Thunderdropmusic/MarcaPasos/docs/assets/1775234487619.jpg

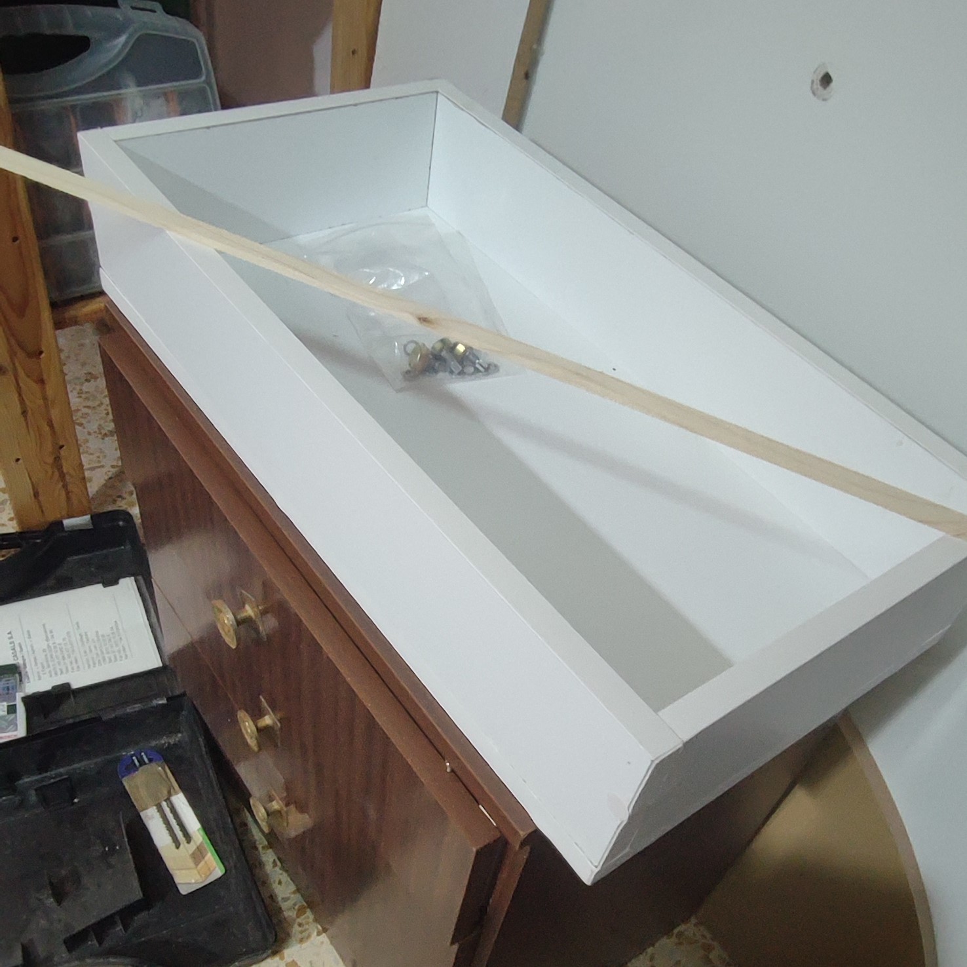
docs/assets/1775234487619.jpg
