Thunderdropmusic/MarcaPasos/docs/assets/1775234487627.jpg

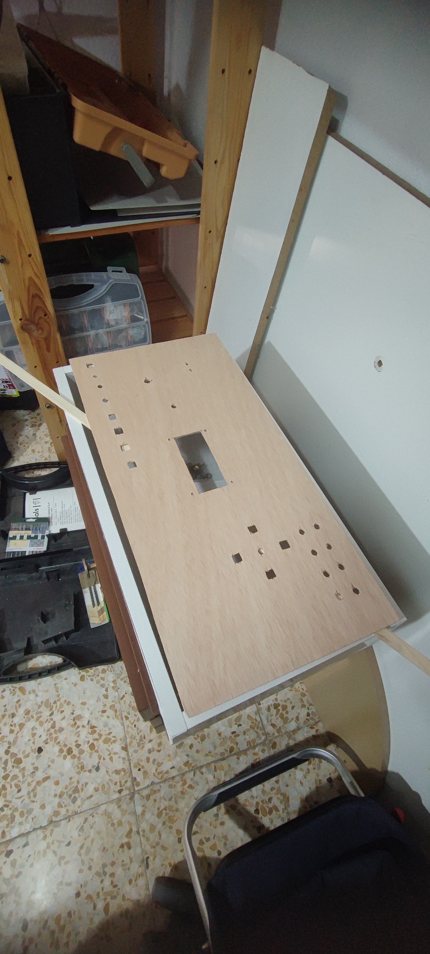
docs/assets/1775234487627.jpg
