Thunderdropmusic/MarcaPasos/docs/assets/1775234487634.jpg

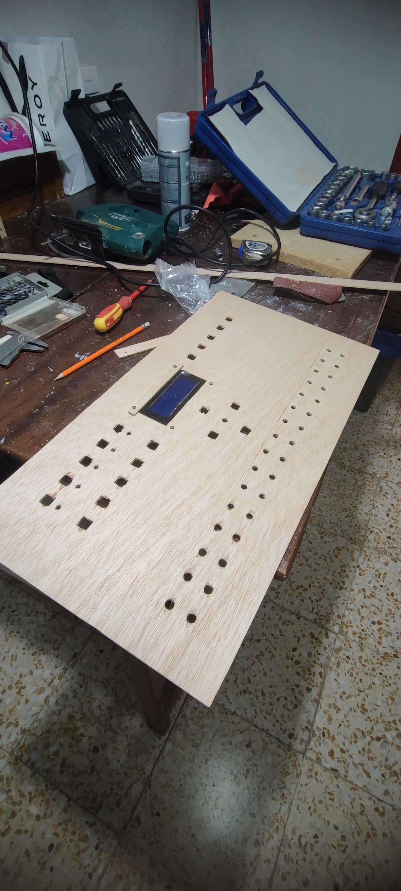
docs/assets/1775234487634.jpg
