Thunderdropmusic/MarcaPasos/docs/assets/1775234487641.jpg

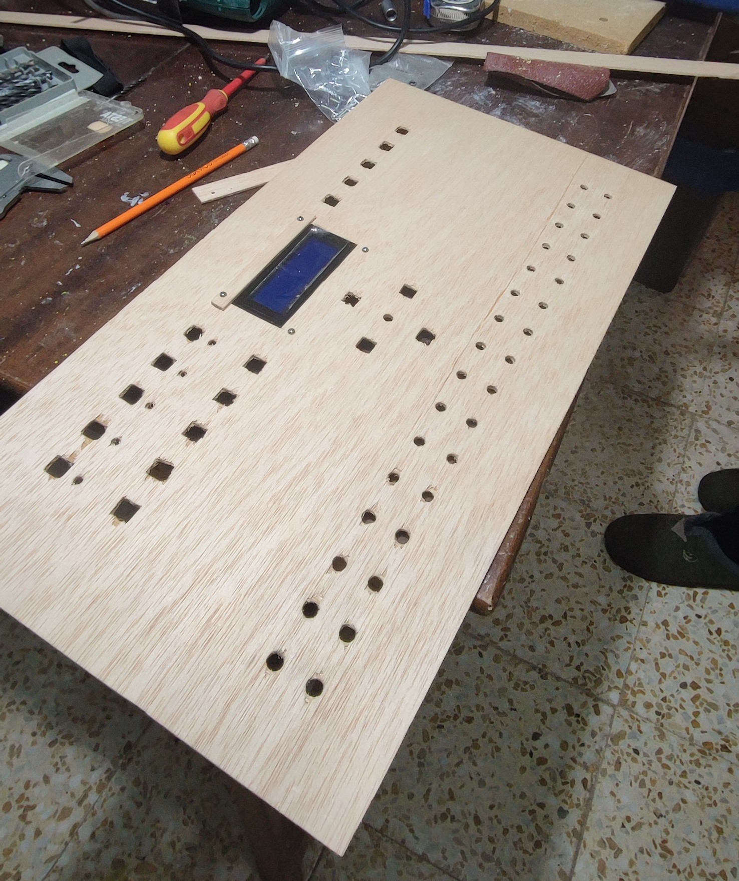
docs/assets/1775234487641.jpg
