Thunderdropmusic/MarcaPasos/docs/assets/1776208259461.jpg

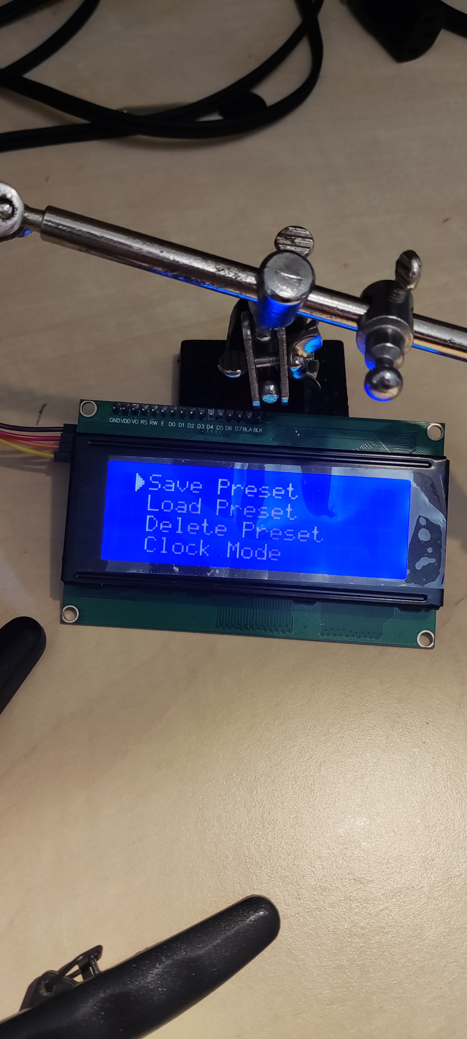
docs/assets/1776208259461.jpg
