Thunderdropmusic/MarcaPasos/docs/assets/1776208259470.jpg

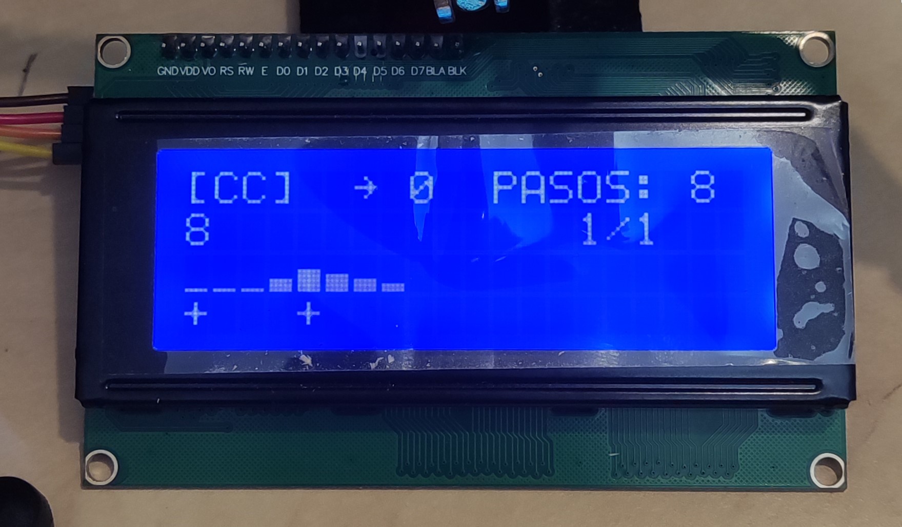
docs/assets/1776208259470.jpg
