Thunderdropmusic/MarcaPasos/docs/assets/1776208259479.jpg

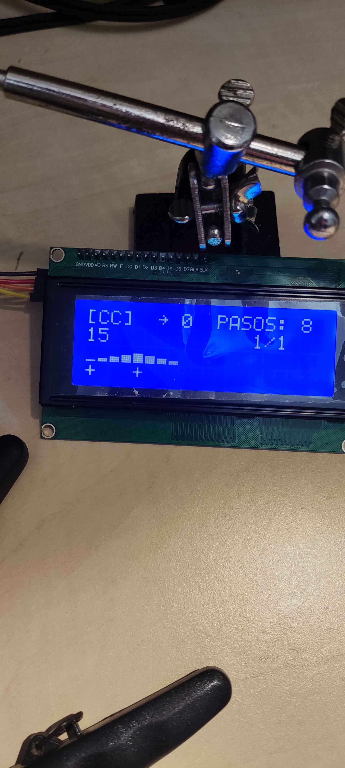
docs/assets/1776208259479.jpg
