Thunderdropmusic/MarcaPasos/docs/assets/1776208259487.jpg

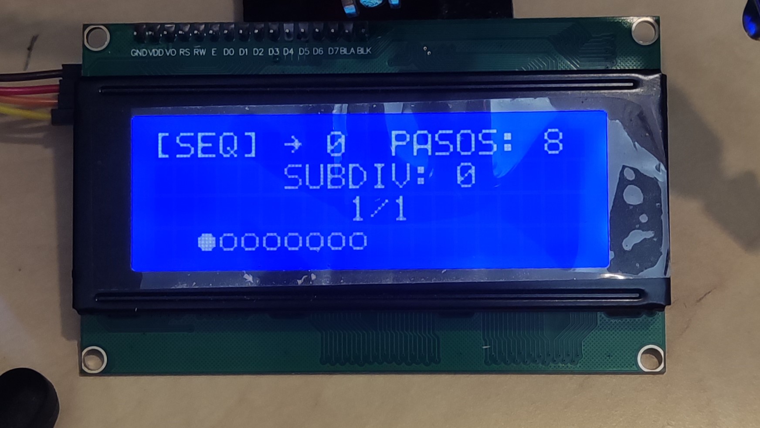
docs/assets/1776208259487.jpg
