Thunderdropmusic/MarcaPasos/docs/assets/1776208259495.jpg

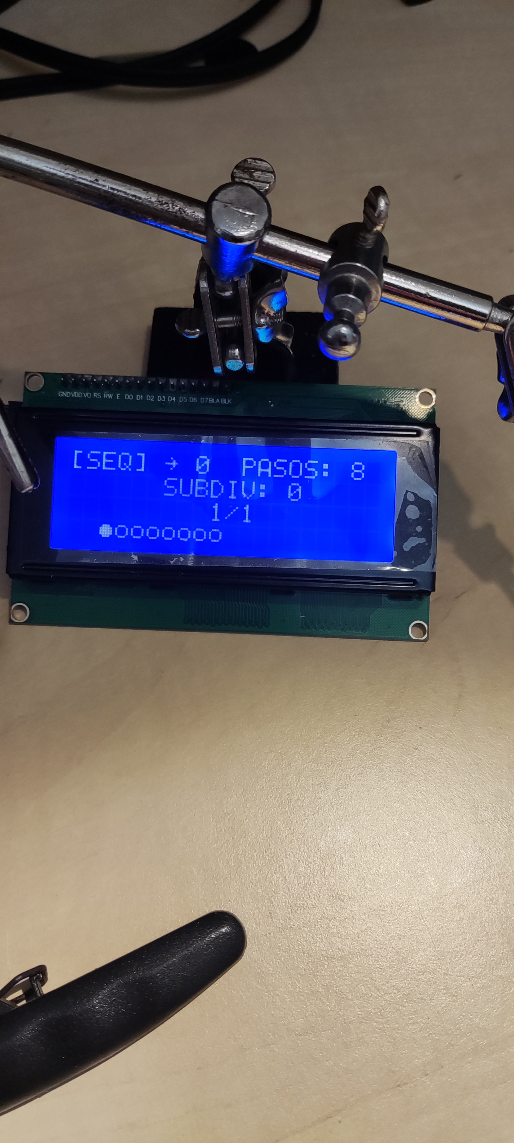
docs/assets/1776208259495.jpg
