Thunderdropmusic/MarcaPasos/docs/assets/1776208259502.jpg

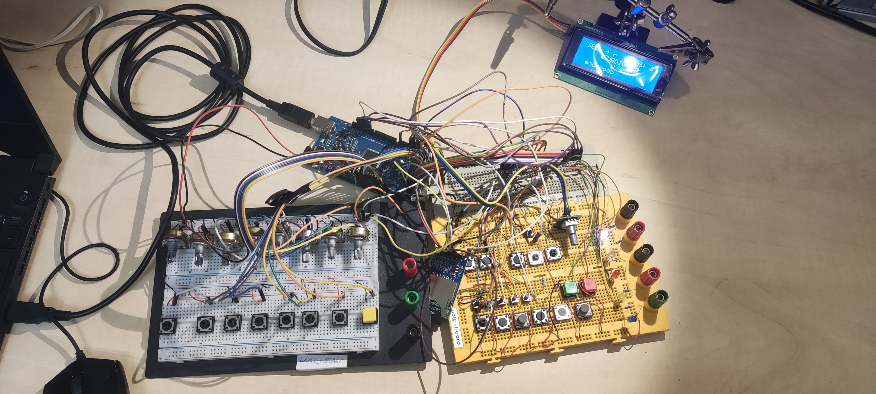
docs/assets/1776208259502.jpg
