Thunderdropmusic/MarcaPasos/docs/assets/1776288896708.jpg

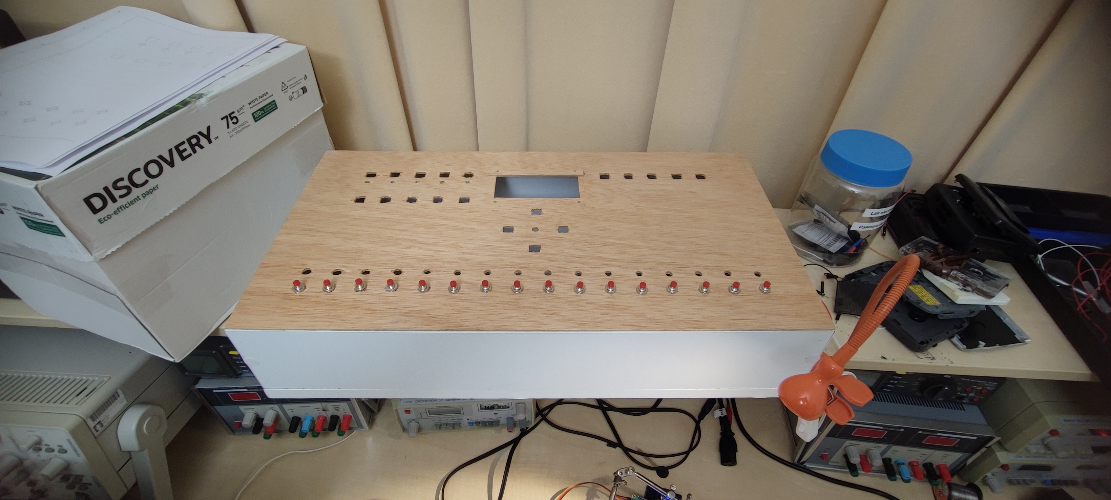
docs/assets/1776288896708.jpg
