Thunderdropmusic/MarcaPasos/docs/assets/1776288896717.jpg

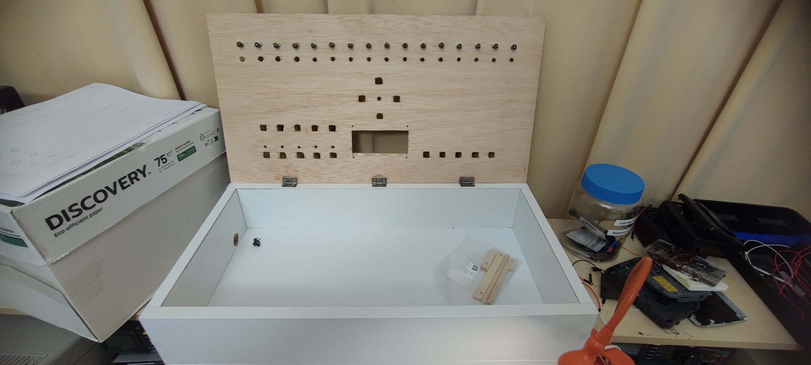
docs/assets/1776288896717.jpg
