Thunderdropmusic/MarcaPasos/docs/assets/1776288896731.jpg

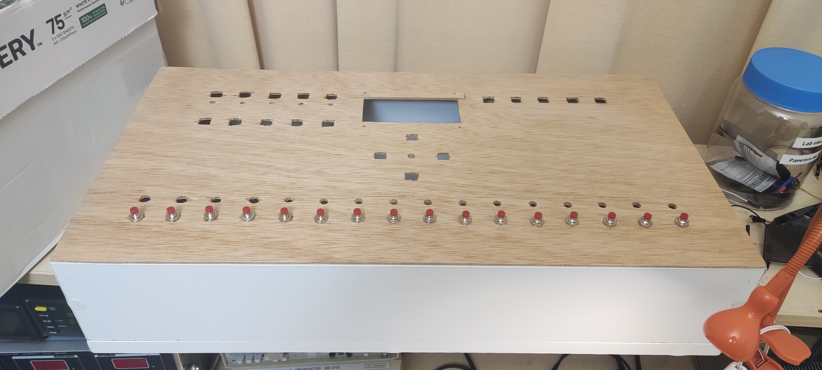
docs/assets/1776288896731.jpg
