Thunderdropmusic/MarcaPasos/docs/assets/1776289153111.jpg

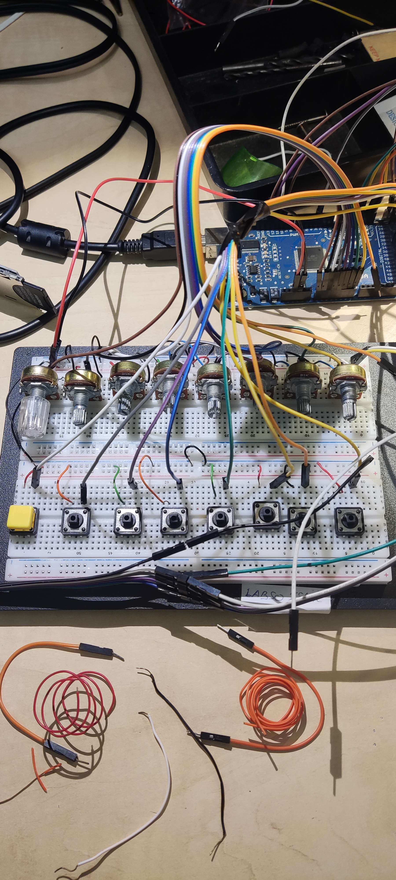
docs/assets/1776289153111.jpg
