Thunderdropmusic/MarcaPasos/docs/assets/1776289153119.jpg

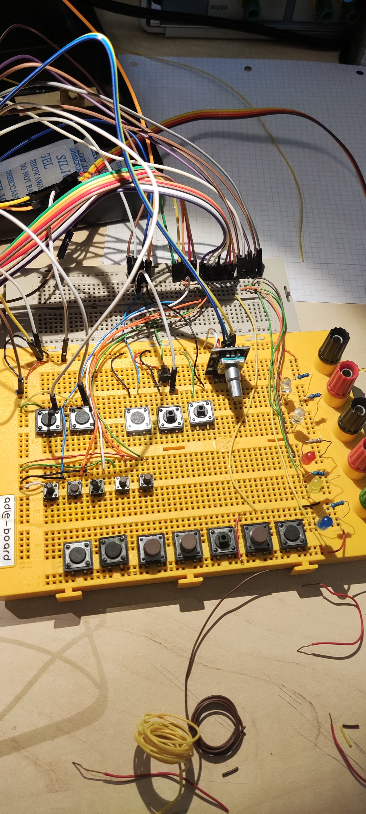
docs/assets/1776289153119.jpg
