Thunderdropmusic/MarcaPasos/docs/assets/1780314757962.jpg

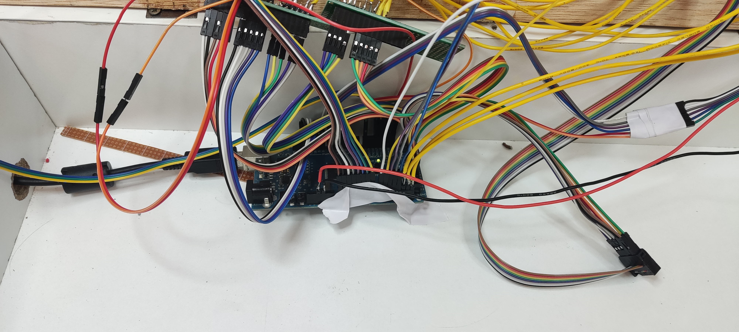
docs/assets/1780314757962.jpg
