Thunderdropmusic/MarcaPasos/docs/assets/1780314757989.jpg

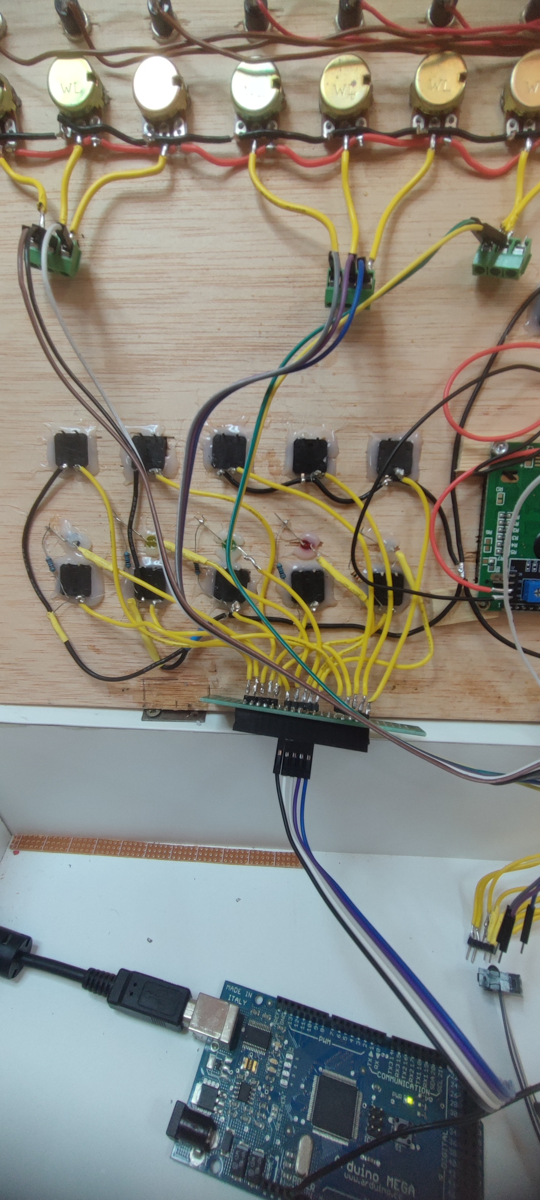
docs/assets/1780314757989.jpg
