Thunderdropmusic/MarcaPasos/docs/assets/1780314758041.jpg

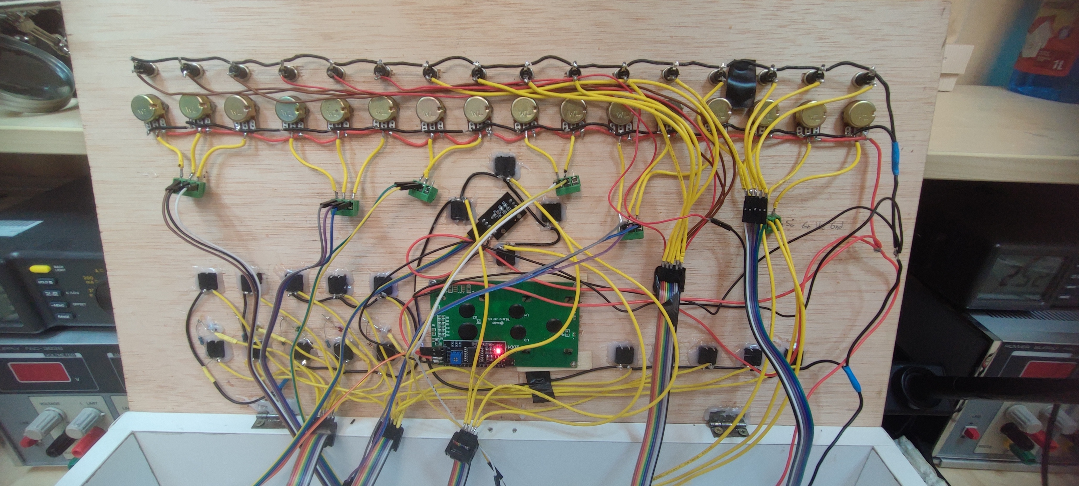
docs/assets/1780314758041.jpg
