Thunderdropmusic/MarcaPasos/docs/assets/1780314758049.jpg

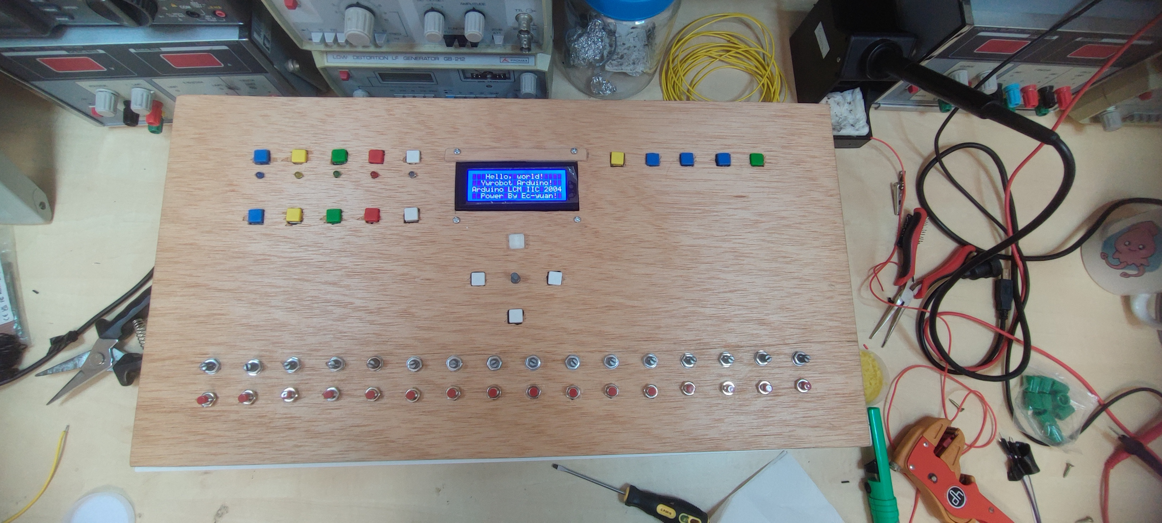
docs/assets/1780314758049.jpg
