Thunderdropmusic/MarcaPasos/docs/assets/1780314758056.jpg

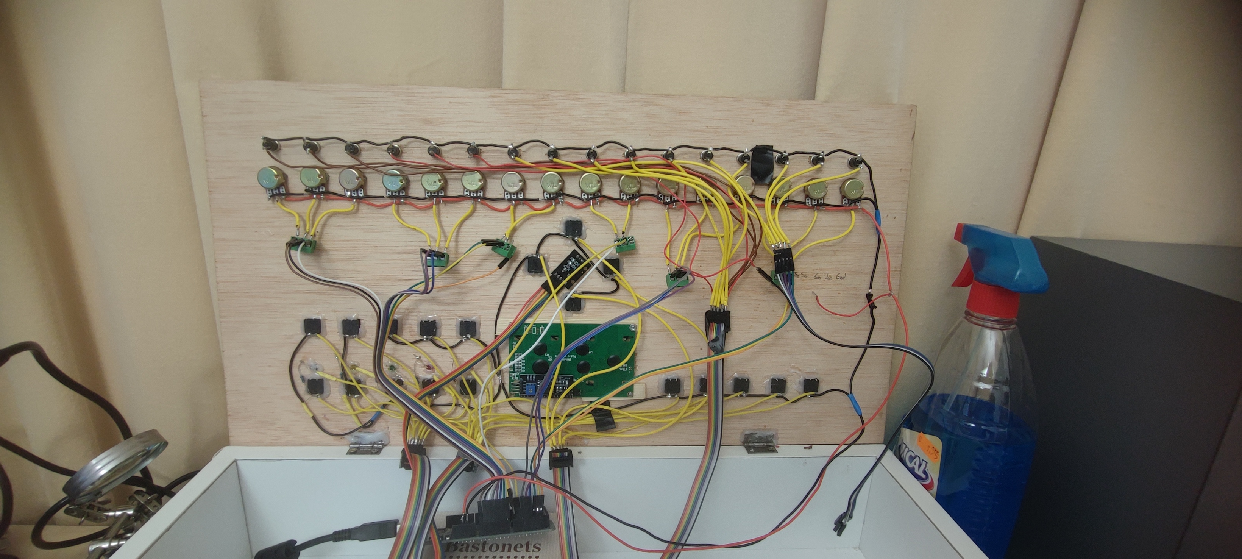
docs/assets/1780314758056.jpg
