Thunderdropmusic/MarcaPasos/docs/assets/1780314758062.jpg

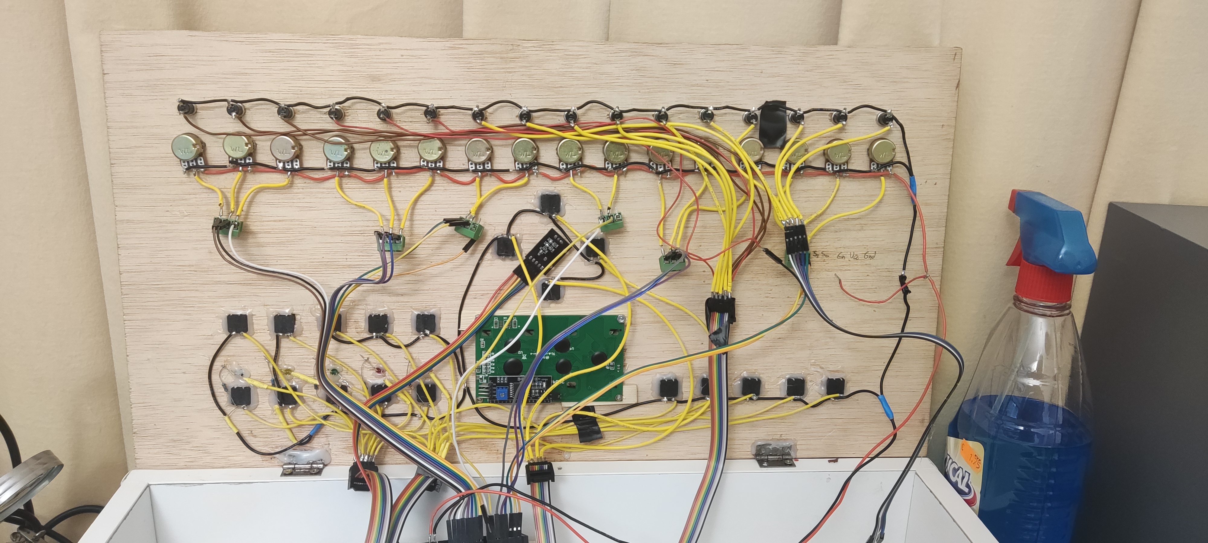
docs/assets/1780314758062.jpg
