Thunderdropmusic/MarcaPasos/docs/assets/1780314758069.jpg

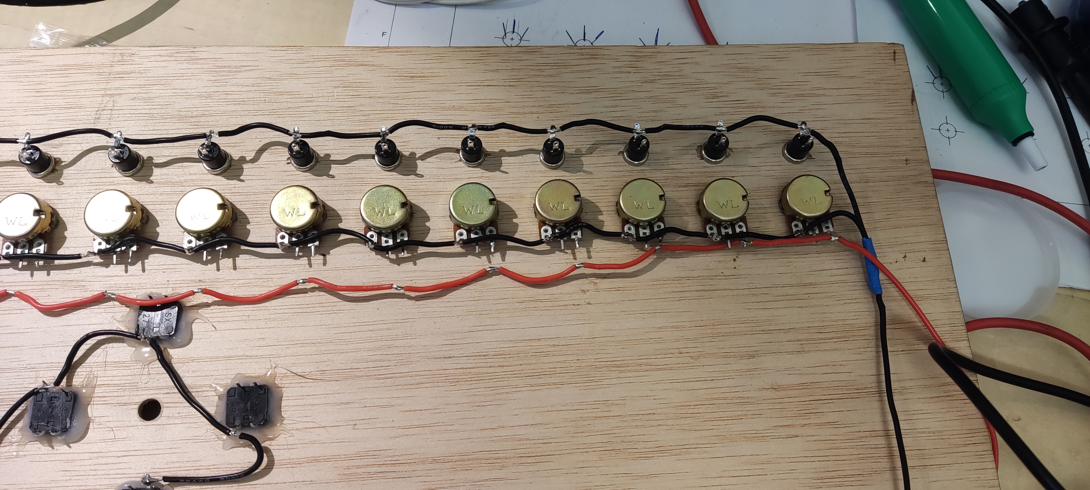
docs/assets/1780314758069.jpg
