Thunderdropmusic/MarcaPasos/docs/assets/1780314758076.jpg

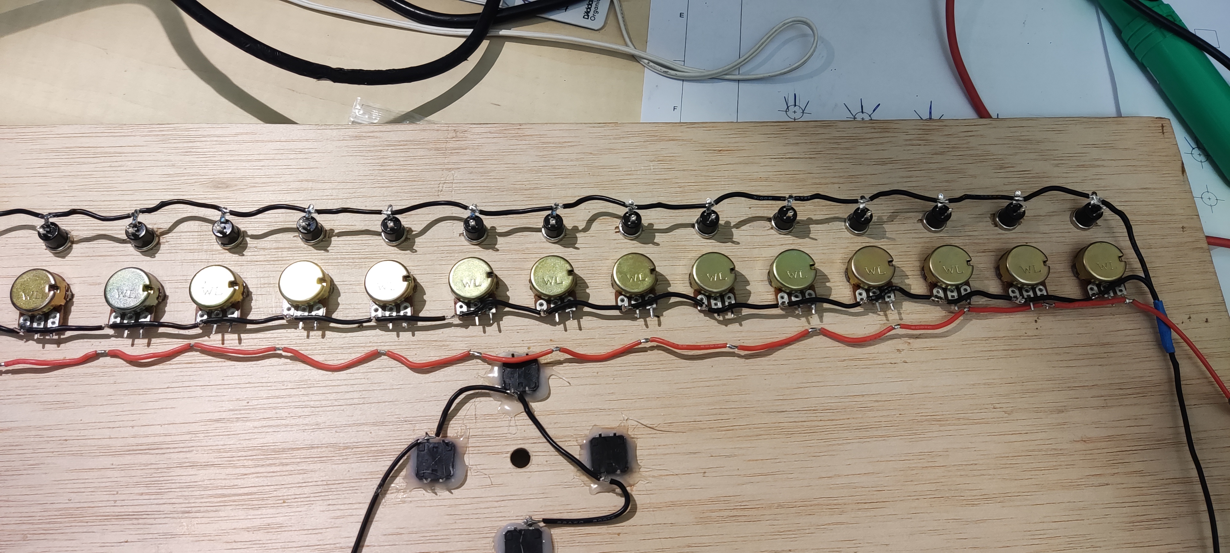
docs/assets/1780314758076.jpg
