Thunderdropmusic/MarcaPasos/docs/assets/1780314758083.jpg

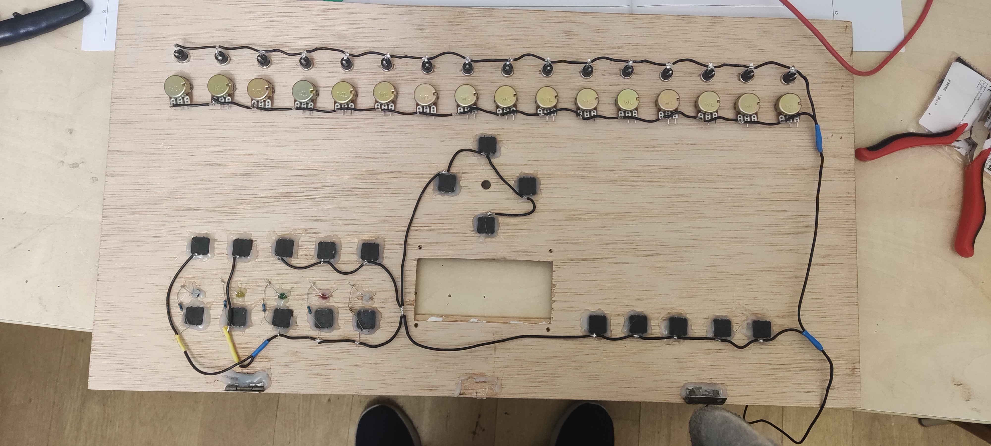
docs/assets/1780314758083.jpg
