Thunderdropmusic/MarcaPasos/docs/assets/1780314758090.jpg

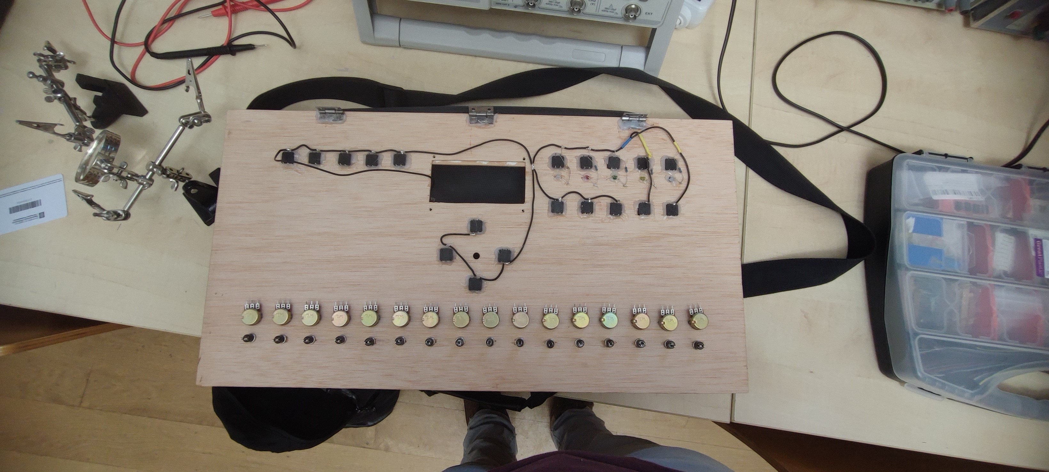
docs/assets/1780314758090.jpg
