Thunderdropmusic/MarcaPasos/Planos/ky-040-enkoder-s-tlacitkem-1.snapshot.1/16558_3.jpg

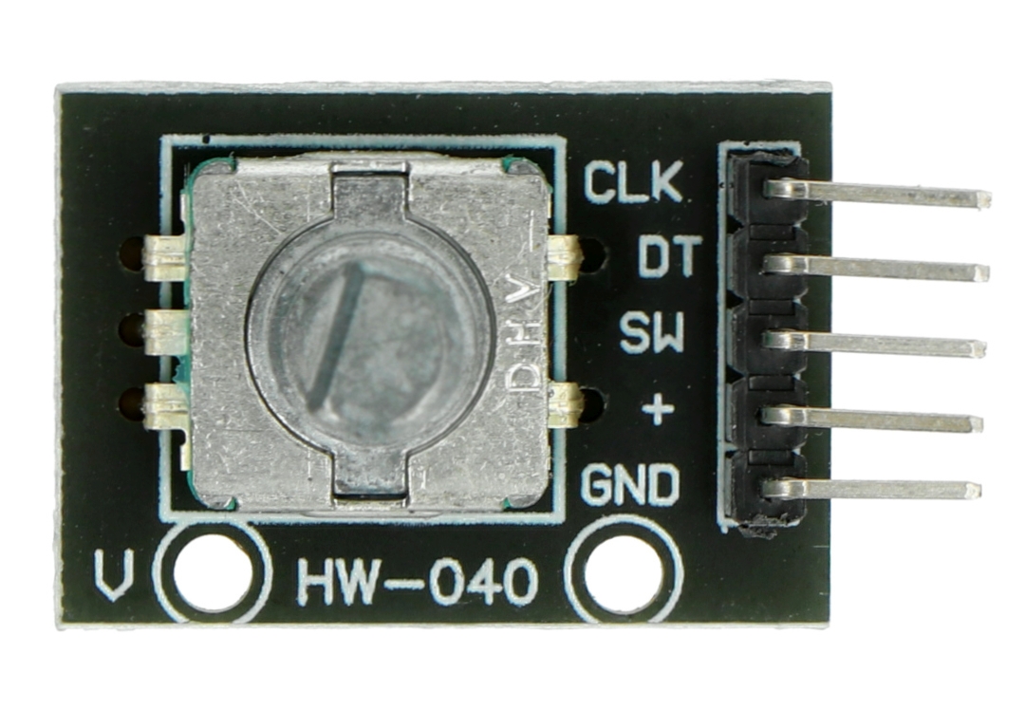
Planos/ky-040-enkoder-s-tlacitkem-1.snapshot.1/16558_3.jpg
