Thunderdropmusic/MarcaPasos/Planos/ky-040-enkoder-s-tlacitkem-1.snapshot.1/420154-9426-1000x1000.jpg

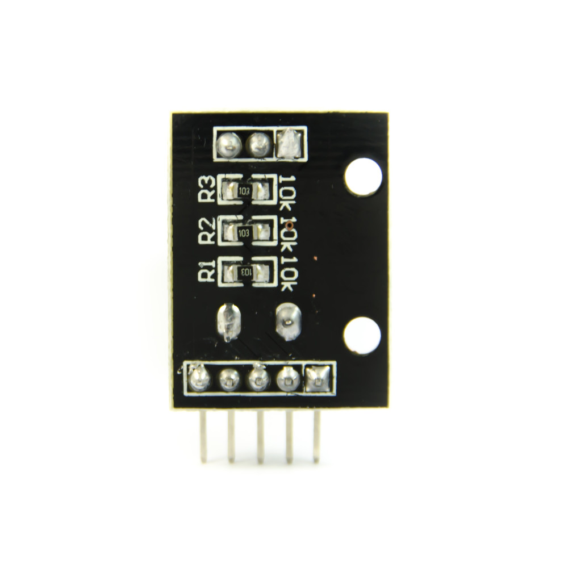
Planos/ky-040-enkoder-s-tlacitkem-1.snapshot.1/420154-9426-1000x1000.jpg
