Thunderdropmusic/MarcaPasos/Planos/lcd-20x4-display-hd44780-arduiono-raspberry-pi-1.snapshot.1/lcd20x4hd44780.jpg

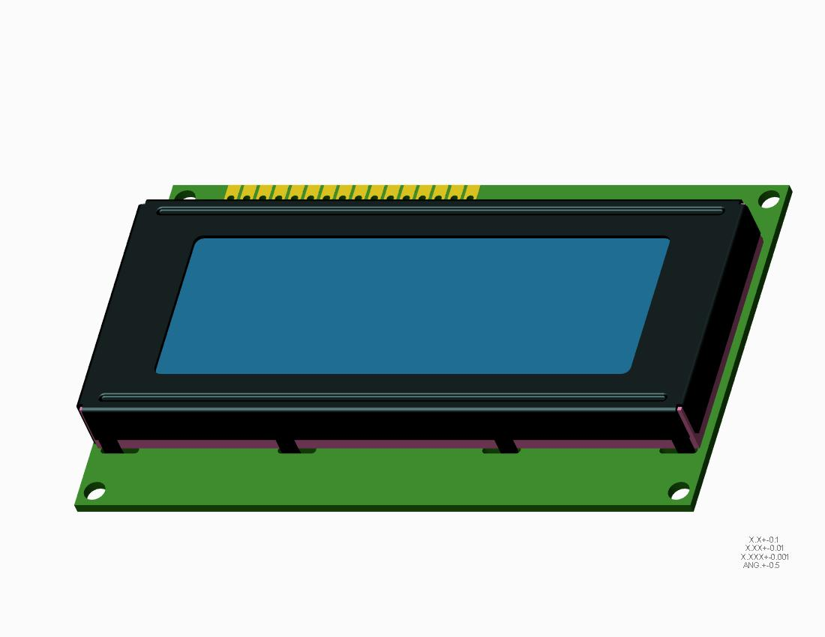
Planos/lcd-20x4-display-hd44780-arduiono-raspberry-pi-1.snapshot.1/lcd20x4hd44780.jpg
