Thunderdropmusic/MarcaPasos/Planos/Plano cortado.jpg

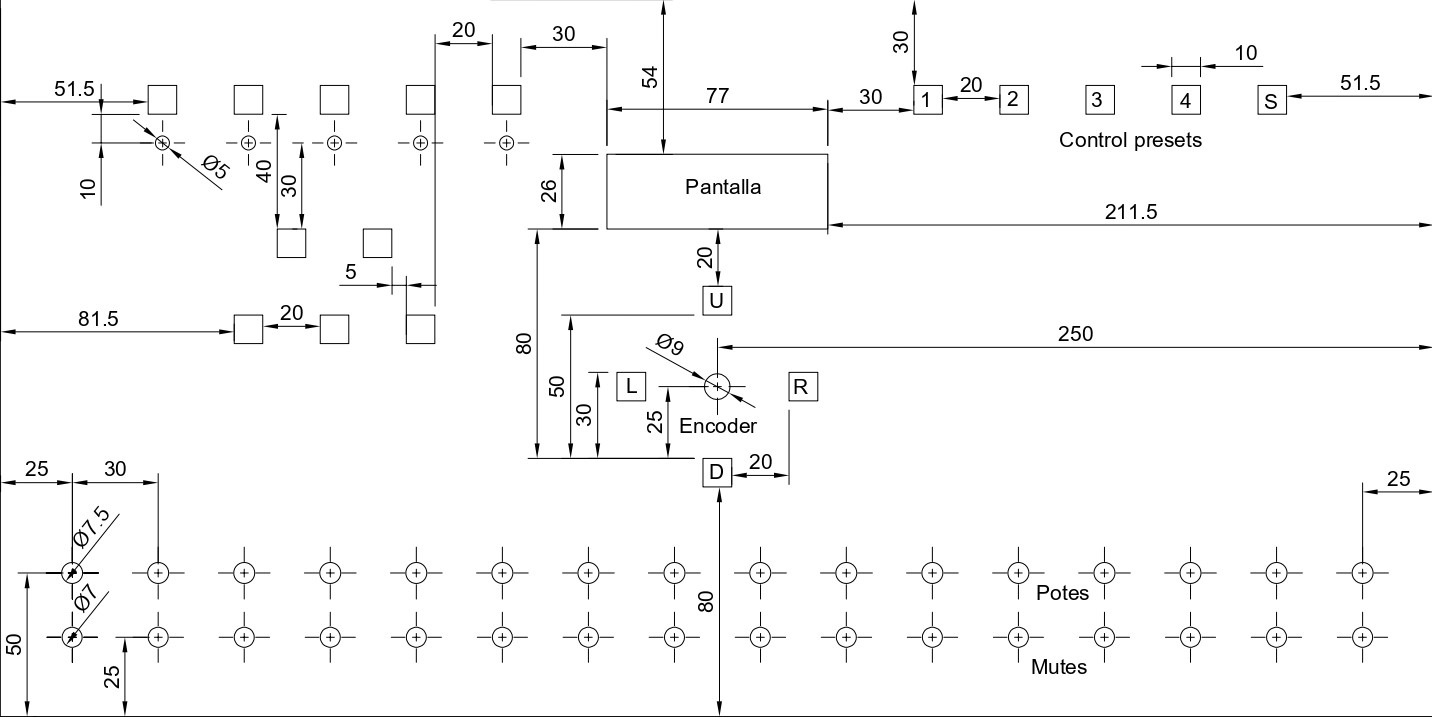
Planos/Plano cortado.jpg
