Thunderdropmusic/MarcaPasos/Planos/Plano v1.2_page-0001.jpg

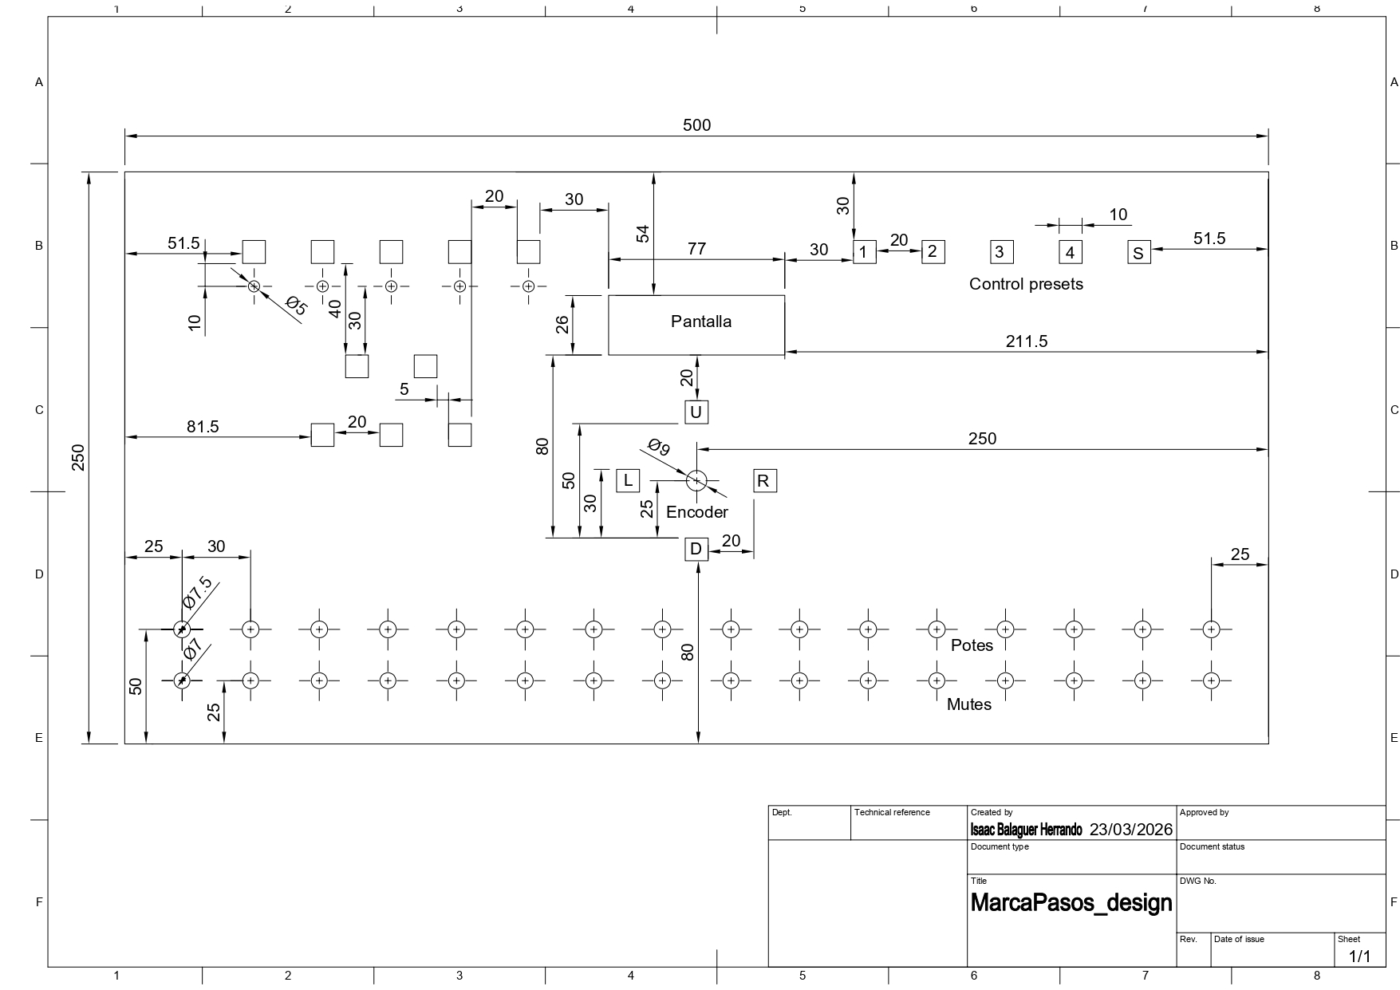
Planos/Plano v1.2_page-0001.jpg
