Thunderdropmusic/MarcaPasos/Planos/PlanosFirtzing_bb.jpg

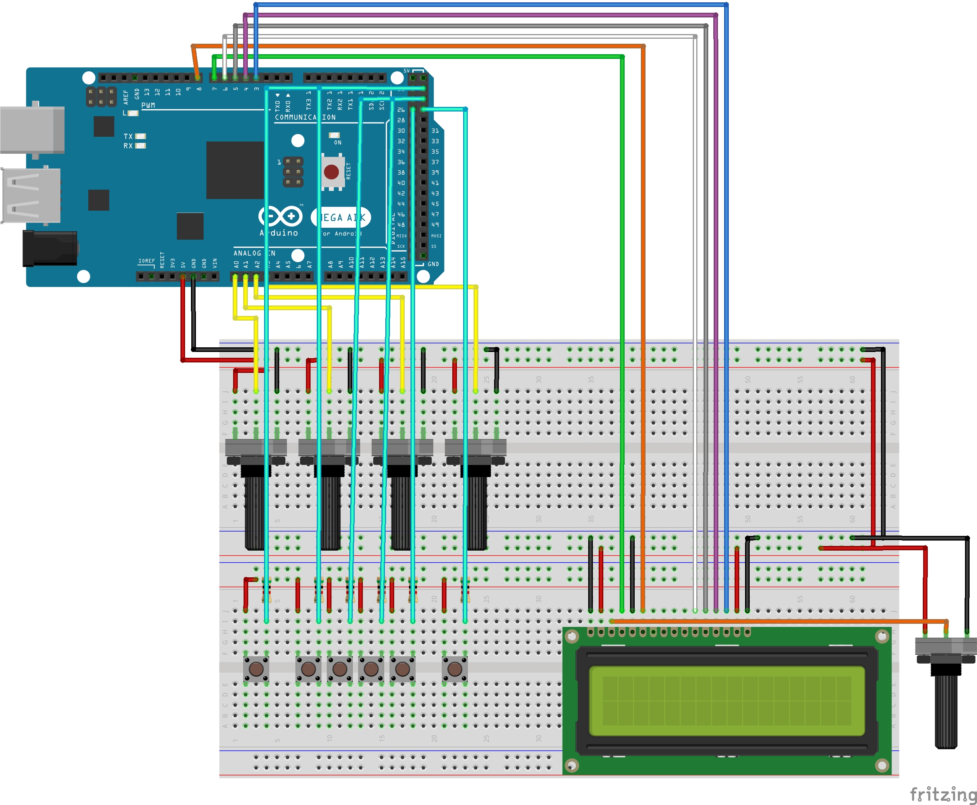
Planos/PlanosFirtzing_bb.jpg
