Thunderdropmusic/MarcaPasos/Planos/rotary-encoder-22.snapshot.2/Screenshot_1.png

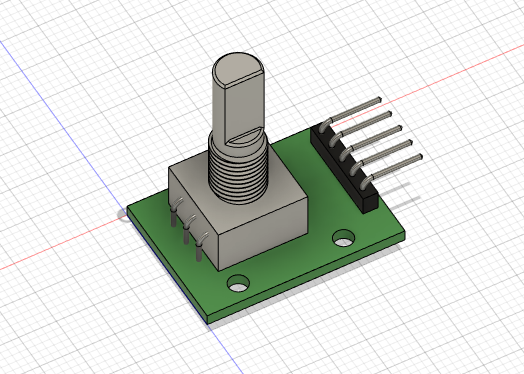
Planos/rotary-encoder-22.snapshot.2/Screenshot_1.png
