Thunderdropmusic/MarcaPasos/Planos/rotary-encoder-arduino-daughter-board-1.snapshot.3/Board2.png

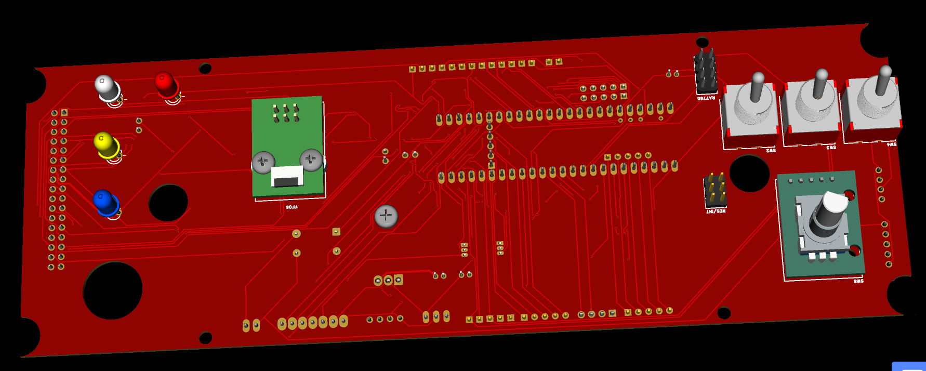
Planos/rotary-encoder-arduino-daughter-board-1.snapshot.3/Board2.png
