Thunderdropmusic/MarcaPasos/Planos/rotary-encoder-arduino-daughter-board-1.snapshot.3/EncoderPic.png

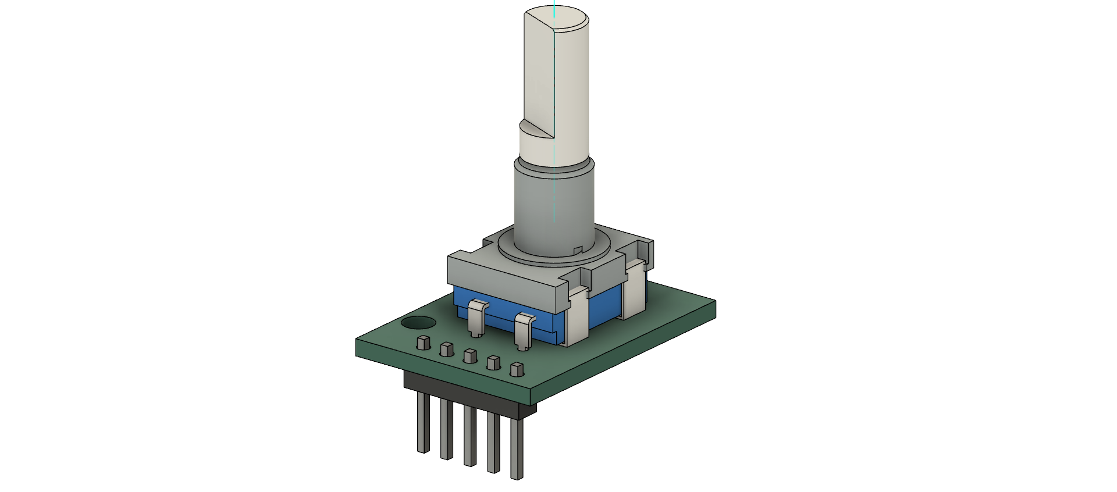
Planos/rotary-encoder-arduino-daughter-board-1.snapshot.3/EncoderPic.png
