Thunderdropmusic/MarcaPasos/Planos/rotary-encoder-arduino-daughter-board-1.snapshot.3/My encoder dimensions.png

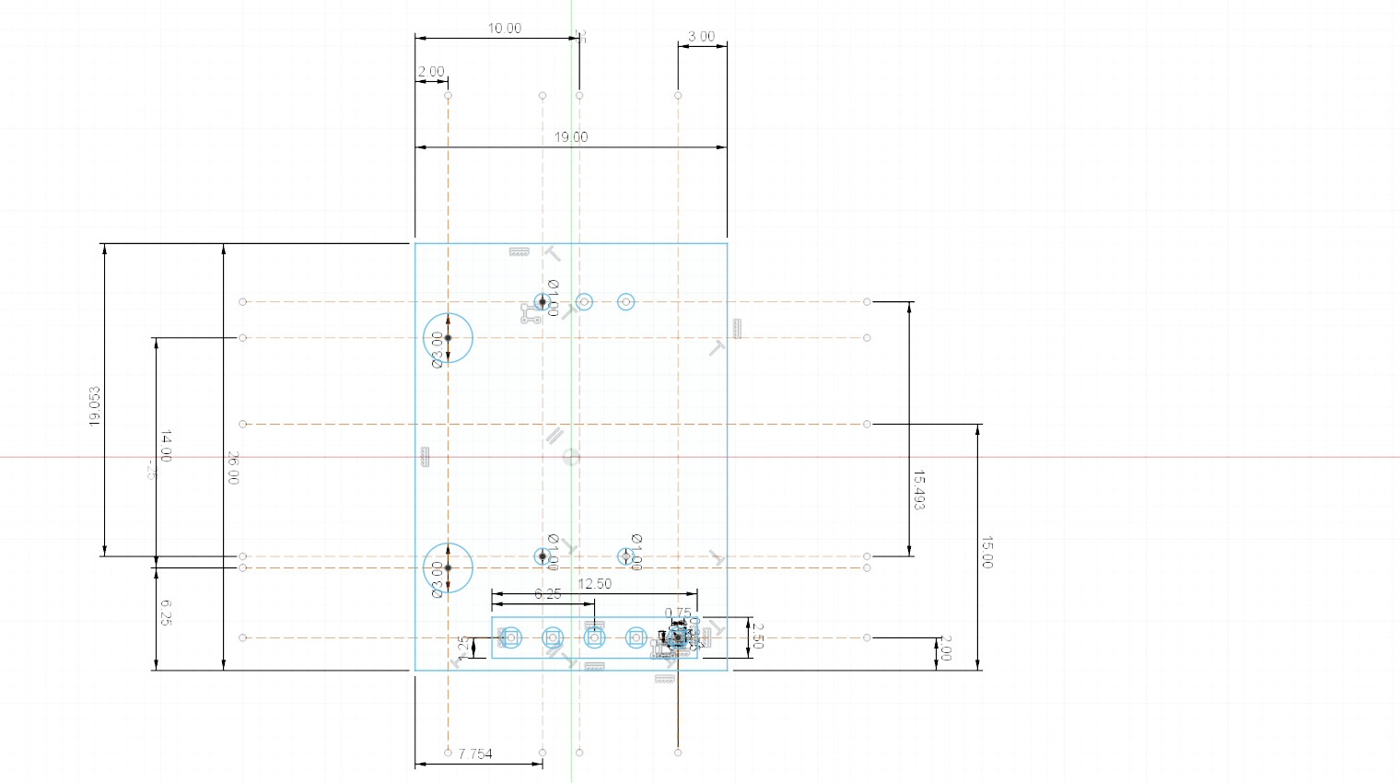
Planos/rotary-encoder-arduino-daughter-board-1.snapshot.3/My encoder dimensions.png
