Thunderdropmusic/MarcaPasos/research/2026-04-11_MarcaPasos_slot_made_extension/midiPrograming.cpp

#include <Arduino.h>
#include <MIDI.h>
#include "MidiProgramming.h"
#include "menus_buttons.h"
#include "midiInterface.h"
#include "midiPresets.h"
#include "draw_menus.h"
#include "config.h"


// Declaración de la instancia
extern midi::MidiInterface<midi::SerialMIDI<HardwareSerial, HairlessConfig>> MIDI;

MidiProgramming midiProg[N_MAX_SEQS] = {
    MidiProgramming(0), 
    MidiProgramming(1), 
    MidiProgramming(2), 
    MidiProgramming(3), 
    MidiProgramming(4)
};
byte MidiProgramming::tipoMsgMidi = 0;
byte MidiProgramming::modeMidiClock = 0;
bool MidiProgramming::flagArmed[N_MAX_SEQS] = {false, false, false, false, false};

const byte MidiProgramming::escalasNotas[5][13]{
  {0, 1, 2, 3, 4, 5, 6, 7, 8, 9, 10, 11, 12}, //Escala cromática
  {0, 2, 3, 5, 7, 8, 10, 12, 0, 0, 0, 0, 0}, //Escala menor Natural
  {0, 2, 4, 5, 7, 9, 11, 12, 0, 0, 0, 0, 0}, //Escala Mayor
  {0, 2, 4, 6, 8, 10, 12, 0, 0, 0, 0, 0, 0}, //Escala de tonos
  {0, 1, 3, 4, 6, 7, 9, 10, 12, 0, 0, 0, 0} //Escala Semitono-tono
};

const byte MidiProgramming::subdivisionesArray[12] {3, 4, 6, 8, 12, 16, 24, 32, 48, 64, 96};

const byte MidiProgramming::subdivisionesComplejasArray[3][6] {
  {5, 7, 9, 11, 13, 15},
  {10, 14, 18, 22, 26, 30},
  {20, 28, 36, 0, 0, 0,}
};
const byte MidiProgramming::nNotasEscalas[5]{13, 8, 8, 7, 9};

MidiProgramming::MidiProgramming(byte _id) : 
  id(_id)


  //variables MIDI y notas
{
  decay = 250;
  microsSubdivision = 50000000;
  tempo = 120;
  tempoMicros = int(60000000/(tempo*24.0));
  seqActual = inExtension ? &p->seq_extension[id] : &p->nSequence[id];
}

void MidiProgramming::midiSeq(){
  if(tipoMsgMidi == 0xFA){ //Start
    if(modeMidiClock == 1){
      MIDI.sendRealTime(midi::Start);
    }
    notaFuera = false;
    play = true;
    nClockMsg = 0;
    pulsoClock = 0;
    tiempoClock1 = 0;
    tiempoClock2 = 0;
    lecturaPulsoClock = 24;
    primeraMedicionSubCompleja = true;
    nStep = 0;
    if(seqActual->subdivMode == 2){
      microsSubdivision = 0;
    }
    else{subdivision = subdivisionesArray[seqActual->indexSubdivisiones];
    }
  }
  else if(tipoMsgMidi == 0xF8){
    if(seqActual->subdivMode == 0 || seqActual->subdivMode == 1){
      modo01Subdivision();
    }
    else if(seqActual->subdivMode == 2){
      modo2Subdivision();
    }
  }
  else if(tipoMsgMidi == 0xFC){ //Stop
    play = false;
    if(modeMidiClock == 1){MIDI.sendRealTime(midi::Stop);}
  }
}

void MidiProgramming::initMode(){
  nClockMsg = 0;
  pulsoClock = 0;
  tiempoClock1 = 0;
  tiempoClock2 = 0;
  lecturaPulsoClock = 24;
  primeraMedicionSubCompleja = true;
  nStep = 0;
  microsSubdivision = 0;
}

void MidiProgramming::modo01Subdivision(){
  if (subdivision < 16 || subdivision == 24){
    if(pulsoClock == 24){
      pulsoClock = 0, subdivision = subdivisionesArray[seqActual->indexSubdivisiones], nClockMsg = 0;
      if(flagArmed[id]){
        seqActual->armed = true;
        flagArmed[id] = false;
      }
    }
  }
  else{
    if(pulsoClock == 96){
      pulsoClock = 0, subdivision = subdivisionesArray[seqActual->indexSubdivisiones], nClockMsg = 0;
      if(flagArmed[id]){
        seqActual->armed = true;
        flagArmed[id] = false;
      }
    }
  }
  if(menusUI.cambioModo2[id] && pulsoClock == 0){
    seqActual->subdivMode = 2;
    initMode();
    menusUI.cambioModo2[id] = false;
    drawUI.updateLCD = true;
    modo2Subdivision();
    return;
  }
  nClockMsg++;
  pulsoClock++;
  if (nClockMsg == subdivision){
    decay = 10*subdivision;
    nClockMsg = 0;
    nStep ++;
    if (nStep > seqActual->nTotalSteps - 1){
      nStep = 0;
      if (p->nSequence[id].extensionArmed) {
        inExtension = !inExtension;
      }
      else {inExtension = false;}
      seqActual = inExtension ? &p->seq_extension[id] : &p->nSequence[id];
      if(seqActual->subdivMode == 0 || seqActual->subdivMode == 1){subdivision = subdivisionesArray[seqActual->indexSubdivisiones];}
      else{subdivision = subdivisionesComplejasArray[seqActual->indComplexSubdivY][seqActual->indComplexSubdivX];}
      pulsoClock = 0;
      nClockMsg = 0;
    }
  }
}

void MidiProgramming::modo2Subdivision(){
    if(menusUI.cambioModo0[id] && pulsoClock == 0){
      seqActual->subdivMode = 0;
      initMode();
      menusUI.cambioModo0[id] = false;
      drawUI.updateLCD = true;
      modo01Subdivision();
      return;
    }
    if(menusUI.cambioModo1[id] && pulsoClock == 0){
      seqActual->subdivMode = 1;
      initMode();
      menusUI.cambioModo1[id] = false;
      drawUI.updateLCD = true;
      modo01Subdivision();
      return;
    }
    nClockMsg++;
  if(pulsoClock == 0){
    subdivision = subdivisionesComplejasArray[seqActual->indComplexSubdivY][seqActual->indComplexSubdivX];
    tiempoClock1  = micros();
    if (tiempoClock2 != 0 && nClockMsg > 1) {
      sumaTiempos = tiempoClock1 - tiempoClock2;
      if(primeraMedicionSubCompleja){microsSubdivision = sumaTiempos*4 / subdivision;}
      else{microsSubdivision = sumaTiempos / subdivision;}
      tiempoUltimaNota = tiempoClock1;
      primerPulso = true;
      primeraMedicionSubCompleja = false;
    }
    tiempoClock2 = tiempoClock1;
  } 
  pulsoClock++;
  if(pulsoClock >= lecturaPulsoClock){
    pulsoClock = 0;
    lecturaPulsoClock = 96;
  }
}

void MidiProgramming::midiNotesOn(){
 //el pote controla la nota del midi
  if(play == true && !notaFuera && (seqActual->subdivMode == 0 || seqActual->subdivMode == 1)){
    if (nClockMsg == 0){ 
      notaFuera = true;
      if(!seqActual->steps[nStep].mutes){
        MIDI.sendNoteOn(seqActual->steps[nStep].note + (12 * seqActual->steps[nStep].octave), seqActual->steps[nStep].velocity, id + 1);
        notaTocada = seqActual->steps[nStep].note + 12 * seqActual->steps[nStep].octave;
      }
      timeDecayNote = millis();
    }
  }
  else if(play == true && seqActual->subdivMode == 2){
    if(primerPulso){
      tiempoUltimaNota = tiempoClock1;
      primerPulso = false; 
      dispararNotaMode2();
    }
    else if (microsSubdivision >= 10000 && (tiempoActualMicros - tiempoUltimaNota > microsSubdivision)){
      unsigned long tiempoDesdeInicioRedonda = tiempoActualMicros - tiempoClock1;
      unsigned long duracionRedondaTeorica = microsSubdivision * subdivision;
      if (tiempoDesdeInicioRedonda < (duracionRedondaTeorica - 15000)) {
        tiempoUltimaNota += microsSubdivision;
        dispararNotaMode2();
      }
    }
  }
}


void MidiProgramming::dispararNotaMode2(){ 
  notaFuera = true;
  if(!seqActual->steps[nStep].mutes){
    MIDI.sendNoteOn(seqActual->steps[nStep].note + (12 * seqActual->steps[nStep].octave), seqActual->steps[nStep].velocity, id + 1);
  }
  decay = (microsSubdivision/2000);
  notaTocada = seqActual->steps[nStep].note + 12 * seqActual->steps[nStep].octave;
  timeDecayNote = millis();
  nStep ++;
  if (nStep > seqActual->nTotalSteps - 1){
    nStep = 0;
    if (p->nSequence[id].extensionArmed) {
      inExtension = !inExtension;
    }
    else {inExtension = false;}
    seqActual = inExtension ? &p->seq_extension[id] : &p->nSequence[id];
    if(seqActual->subdivMode == 0 || seqActual->subdivMode == 1){subdivision = subdivisionesArray[seqActual->indexSubdivisiones];}
    else{subdivision = subdivisionesComplejasArray[seqActual->indComplexSubdivY][seqActual->indComplexSubdivX];}
    pulsoClock = 0;
    nClockMsg = 0;
  }
}

void MidiProgramming::midiNotesOff(){
  if (notaFuera && (millis() - timeDecayNote >= decay)){
    MIDI.sendNoteOff(notaTocada, 0, id + 1);
    notaFuera = false;
    timeDecayNote = 0;
  }
}

int MidiProgramming::ccCurveFunction(int i, int subdivisionActual, int tensionMode){
  int indiceLUT = (i * 99) / (subdivisionActual - 1);
  byte factorCurva = pgm_read_byte(&(smoothCurves[tensionMode][indiceLUT]));
  return factorCurva;
}

void MidiProgramming::CCSend(){
  if(!play) return;
  else if (tipoMsgMidi != 0xF8 && tipoMsgMidi != 0xFA) return;
  
  if (nClockMsg == 0) {
    nMsgCC[id] = 0;
    int totalSteps = seqActual->nTotalSteps;

    // 1. Buscar el punto desde el que partimos
    int prevStep = nStep;
    int countBack = 0;
    while (countBack < totalSteps) {
      if (!seqActual->steps[prevStep].ccMutes) {
        break; // ¡Encontrado!
      }
      prevStep--;
      if (prevStep < 0) {prevStep = totalSteps - 1;}
      countBack++;
    }

    // 2. Buscar el siguiente punto a interpolar
    int nextStep = nStep + 1;
    if (nextStep >= totalSteps) nextStep = 0;
    int countForward = 0;
    while (countForward < totalSteps) {
      if (!seqActual->steps[nextStep].ccMutes) {
        break; // ¡Encontrado!
      }
      nextStep++;
      if (nextStep >= totalSteps) nextStep = 0; // Wrap-around hacia adelante
      countForward++;
    }

    // 3. Coger los valores de las anclas
    int valorActual = seqActual->steps[prevStep].ccValue;
    int valorSiguiente = seqActual->steps[nextStep].ccValue;
    int ccStepSize = valorSiguiente - valorActual;

    // 4. Calcular distancias reales
    int distanceSteps = 0;
    if (nextStep > prevStep) {distanceSteps = nextStep - prevStep;} 
    else if (nextStep < prevStep) {distanceSteps = (totalSteps - prevStep) + nextStep;} 
    else {distanceSteps = totalSteps;}

    int offsetSteps = 0;
    if (nStep >= prevStep) {offsetSteps = nStep - prevStep;} 
    else {offsetSteps = (totalSteps - prevStep) + nStep;}


    int subdivisionActual = distanceSteps * subdivision;
    int offset = offsetSteps * subdivision; 
    int divisor = (subdivisionActual > 1) ? subdivisionActual : 2; 

    for(int i = 0; i < subdivision; i++) {
      int indexCurva = offset + i;
      long valorCurva = ccCurveFunction(indexCurva, divisor, seqActual->steps[prevStep].ccSmoothCurve);
      CCinterpolation[i] = valorActual + (((long)ccStepSize * valorCurva) / 255);
    }
  }
  else {
    nMsgCC[id]++;
  }
  
  MIDI.sendControlChange(seqActual->ccNumber, CCinterpolation[nMsgCC[id]], id + 1);
}
