Thunderdropmusic/MarcaPasos/research/2026-03-27_MarcaPasos_CCVisualizer/midiInterface.h

#ifndef MidiInterface_H
#define MidiInterface_H

#define NUM_POTES 8
#define NUM_MUTES 8
#define N_MAX_SEQUENCES 5


#include <Arduino.h>
#include <MIDI.h>

struct Sequence;

extern unsigned long tiempoActualMillis;




class MidiInterface {
  private:
    Sequence* s;
  public:
    MidiInterface();
    const byte potesPin[NUM_POTES] = {A0, A1, A2, A3, A4, A5, A6, A7/*, A8, A9, A10, A11, A12, A13, A14, A15*/};
    const byte mutesPin[NUM_MUTES] = {30, 31, 32, 33, 34, 35, 36, 37};
    const byte seqPinLed[5] = {10, 11, 12, 13, 3};
    const byte settingsPin = 9;
    const byte seq1PinButton = 40;
    const byte seq2PinButton = 42;
    const byte seq3PinButton = 44;
    const byte seq4PinButton = 46;
    const byte seq5PinButton = 48;
    const byte pinOctRest = 27;
    const byte pinOctPlus = 29;
    int potSaveValue[NUM_POTES];
    bool mutePulsado[NUM_POTES];
    bool muteActivado;
    bool poteMovido;
    bool poteMovidoMutes;
    byte movedPoteValue;
    byte movedPoteNumber;
    byte indexMovedMute;
    unsigned long timeShowPotValue;
    unsigned long timeShowOctValue;
    unsigned long ultimoTiempoBotonMute[NUM_MUTES];
    unsigned long TiempoPulsadoBotonMute[NUM_MUTES];
    unsigned long ultimoTiempoBotonOct;
    unsigned long ultimoTiempoBotonArm;
    bool octPlusPulsed;
    bool octRestPulsed;   
    bool pulsedIndividualOctave;

    byte seqLayer = 0;

    bool seqArmPulsed[5];

    bool seqButton[5];

    bool comandoEnviado;

    //declaracion de funciones
    void checkPotes();
    void checkMutes();
    void syncWithActiveSequence();
    bool timeDebounce(unsigned long boton, int time);
};

extern MidiInterface midiUI;




#endif
