Thunderdropmusic/MarcaPasos/research/2026-02-26_MarcaPasos_Correccion_notas_No_Apagadas/midiInterface.h

#ifndef MIDIINTERFACE_H
#define MIDIINTERFACE_H

#include <Arduino.h>
#include <MIDI.h>

extern const byte potesPin[];
extern const byte mutesPin[];
extern const byte pinOctPlus;
extern const byte pinOctRest;

extern int notesValue[];
extern bool mutesValue[];
extern int octavaValue[];
extern int velocityValue[];
extern int velocitySaveValue[];
extern const int numPotes;
extern const int numMutes;
extern bool mutePulsado[];
extern bool muteActivado;
extern bool poteMovido;
extern bool poteMovidoMutes;
extern int val, movedPoteValue, movedPoteNumber;
extern int indiceMovedMute;
extern unsigned long timeShowPotValue;
extern unsigned long timeShowOctValue;
extern unsigned long tiempoActualMillis;
extern unsigned long ultimoTiempoBotonMute[];
extern unsigned long TiempoPulsadoBotonMute[];
unsigned long ultimoTiempoBotonOct;
extern bool mute;
extern int menuActual;
extern bool updateLCD;

extern int escalaSeleccionada;
extern const int escalasNotas[5][13];
extern const int nNotasEscalas[];

bool octPlusPulsed, octRestPulsed;
bool pulsedIndividualOctave;

//declaracion de funciones
void checkPotes();
void checkMutes();


void checkMutes() {
  bool octPlus = digitalRead(pinOctPlus);
  bool octRest = digitalRead(pinOctRest);

  if (octPlus && !octPlusPulsed) {
    octPlusPulsed = true;
  }
  if (octRest && !octRestPulsed) {
    octRestPulsed = true;
  }

  for (int i = 0; i < numMutes; i++) {
    mute = digitalRead(mutesPin[i]);
    if (mute) {
      if (mutePulsado[i] == false) {
        mutePulsado[i] = true;
        muteActivado = true;
        TiempoPulsadoBotonMute[i] = tiempoActualMillis;
        indiceMovedMute = i;
      }
      /*
      if(mutePulsado[i][0] && mutePulsado[i][1] && octava < 9 && tiempoActualMillis - ultimoTiempoBotonMute[0] > 250 && tiempoActualMillis - ultimoTiempoBotonMute[1] > 250){
        octava ++;
        ultimoTiempoBotonMute[0] = tiempoActualMillis;
        ultimoTiempoBotonMute[1] = tiempoActualMillis;
        timeShowOctValue = tiempoActualMillis;
        menuActual = 4;
        updateLCD = true;
      }
      else if(mutePulsado[i][2] && mutePulsado[i][3] && octava > 0 && tiempoActualMillis - ultimoTiempoBotonMute[2] > 250 && tiempoActualMillis - ultimoTiempoBotonMute[3] > 250){
        octava --;
        ultimoTiempoBotonMute[2] = tiempoActualMillis;
        ultimoTiempoBotonMute[3] = tiempoActualMillis;
        timeShowOctValue = tiempoActualMillis;
        menuActual = 4;
        updateLCD = true;
      }
      */
      if (tiempoActualMillis - TiempoPulsadoBotonMute[i] > 100 && tiempoActualMillis - ultimoTiempoBotonMute[i] > 250) {
        ultimoTiempoBotonMute[i] = tiempoActualMillis;
      }
      if (octPlusPulsed && tiempoActualMillis - ultimoTiempoBotonOct > 500 && octavaValue[i] < 9) {
        ultimoTiempoBotonOct = tiempoActualMillis;
        timeShowOctValue = tiempoActualMillis;
        octavaValue[i]++;
        menuActual = 4;
        updateLCD = true;
        pulsedIndividualOctave = true;
      } else if (octRestPulsed && tiempoActualMillis - ultimoTiempoBotonOct > 500 && octavaValue[i] > 0) {
        ultimoTiempoBotonOct = tiempoActualMillis;
        timeShowOctValue = tiempoActualMillis;
        octavaValue[i]--;
        menuActual = 4;
        updateLCD = true;
        pulsedIndividualOctave = true;
      }
    } 
    else {
      if (mutePulsado[i] == true && !pulsedIndividualOctave && !octPlusPulsed && !octRestPulsed && !poteMovidoMutes) {
        mutesValue[i] = !mutesValue[i];
        updateLCD = true;
        mutePulsado[i] = false;
        muteActivado = false;
      } 
      else if (mutePulsado[i] == true && pulsedIndividualOctave) {
        mutePulsado[i] = false;
        muteActivado = false;
        pulsedIndividualOctave = false;
      }
      else if(mutePulsado[i] == true && poteMovidoMutes){
        mutePulsado[i] = false;
        muteActivado = false;
        poteMovidoMutes = false;

      }
    }
  }
  if (!octPlus && octPlusPulsed && tiempoActualMillis - ultimoTiempoBotonOct > 250) { octPlusPulsed = false; }
  if (!octRest && octRestPulsed && tiempoActualMillis - ultimoTiempoBotonOct > 250) { octRestPulsed = false; }
  if (!muteActivado && octPlusPulsed && tiempoActualMillis - ultimoTiempoBotonOct > 500) {
    ultimoTiempoBotonOct = tiempoActualMillis;
    timeShowOctValue = tiempoActualMillis;
    for (int i = 0; i < numMutes; i++) {
      if(octavaValue[i] < 9){octavaValue[i]++;}
    }
    menuActual = 5;
    updateLCD = true;
  } 
  else if (!muteActivado && octRestPulsed && tiempoActualMillis - ultimoTiempoBotonOct > 500) {
    ultimoTiempoBotonOct = tiempoActualMillis;
    timeShowOctValue = tiempoActualMillis;
    for (int i = 0; i < numMutes; i++) {
      if(octavaValue[i] > 0){octavaValue[i]--;}
    }
    menuActual = 5;
    updateLCD = true;
  }
}



void checkPotes() {
  for (int i = 0; i < numPotes; i++) {
    int val = analogRead(potesPin[i]);
    if(abs(val - potSaveValue[i]) > 20){
      potSaveValue[i] = val;
      if(muteActivado){
        velocityValue[i] = constrain(map(potSaveValue[i], 1018, 30, 0, 127), 0, 127);
        movedPoteValue = velocityValue[i];
        movedPoteNumber = i;
        timeShowPotValue = tiempoActualMillis;
        menuActual = 3;
        updateLCD = true;
        poteMovidoMutes = true;

      }
      else{
        int notaEscala = constrain(map(potSaveValue[i], 1018, 30, 0, nNotasEscalas[escalaSeleccionada] - 1), 0, nNotasEscalas[escalaSeleccionada] - 1);
        notesValue[i] = escalasNotas[escalaSeleccionada][notaEscala];
        movedPoteValue = notesValue[i];
        movedPoteNumber = i;
        timeShowPotValue = tiempoActualMillis;
        menuActual = 3;
        updateLCD = true;
      }
    }
  }
}

#endif
