Thunderdropmusic/MarcaPasos/research/2026-03-27_MarcaPasos_CCVisualizer/menus_buttons.h

#ifndef MENUS_BUTTONS_H
#define MENUS_BUTTONS_H

#include <Arduino.h>
#include "config.h"

struct Sequence;

extern unsigned long tiempoActualMillis;



class MenusButtons {
  private:
    Sequence* s;

    //Funciones del selector y gestion pantallas
    void gestionarMenu1(); //Notas
    void gestionarMenu2(); //CC
    void selectorEditMode();
    void selectorModoSubdivisiones();
    void selectorSubdivisiones();
    void gestionSubdivGlobal();
    void gestionSubdivBinaria();
    void gestionSubdivCompleja();
    void selectorPasos();
    void selectorClock();

    void selectorNumeroSeqCC();
  public:
  MenusButtons();
  //Variables pines
    const byte pinButton1 = 22; // Arriba
    const byte pinButton2 = 23; // OK / Entrar
    const byte pinButton3 = 24; // Izquierda
    const byte pinButton4 = 25; // Abajo
    const byte pinButton5 = 26; // Derecha

    // Bool Botones
    bool btnArriba;
    bool btnOk;
    bool btnAbajo;
    bool btnIzquierda;
    bool btnDerecha;


    // Variables Navegacion
    byte menuActual;
    byte menuAnterior;
    byte seleccion;
    byte selectNum;
    byte selectDen;

    // Variables indicies subdivisiones
    byte ultimaConfiguracionModo0;
    byte ultimaConfiguracionModo1;
    byte ultimaConfiguracionModo2[2];
    bool cambioModo0[N_MAX_SEQS];
    bool cambioModo1[N_MAX_SEQS];
    bool cambioModo2[N_MAX_SEQS];

    // Variables Enconder
    long posicionActual;
    long posicionAnterior;
    bool rollDerecha;
    bool rollIzquierda;
    // Variables de control
    bool repeatedButton;

    // Variables de tiempo real
    unsigned long ultimoTiempoBotonMenu;

    //Declaración funciones
    bool timeDebounce();
    void syncWithActiveSequence();
    void aplicarCambiosBotones();
    void aplicarCambiosEncoder();
    void checkSeqMode();
    void resetEncoder();
    void checkButtons();
    void showPotes();


};
extern MenusButtons menusUI;
extern void funcionInterrupcion();

#endif
